hiramrodriguez14/Load-UI_MCU/mylib/WSON-6_2x2.step

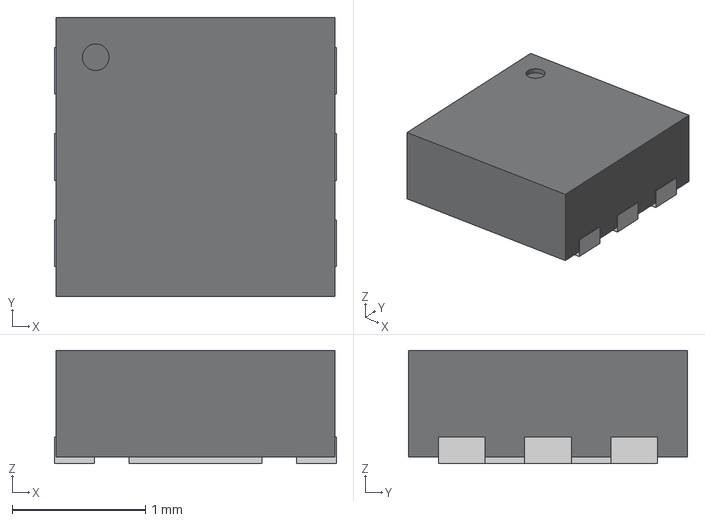
[picture p21: CAD file, 2026-04-30]
mylib/WSON-6_2x2.step
2.12 x 2.10 x 0.85 mm
Pads
