hiramrodriguez14/Load-UI_MCU/mylib/JST_3D/JST-XH4-SMD.step

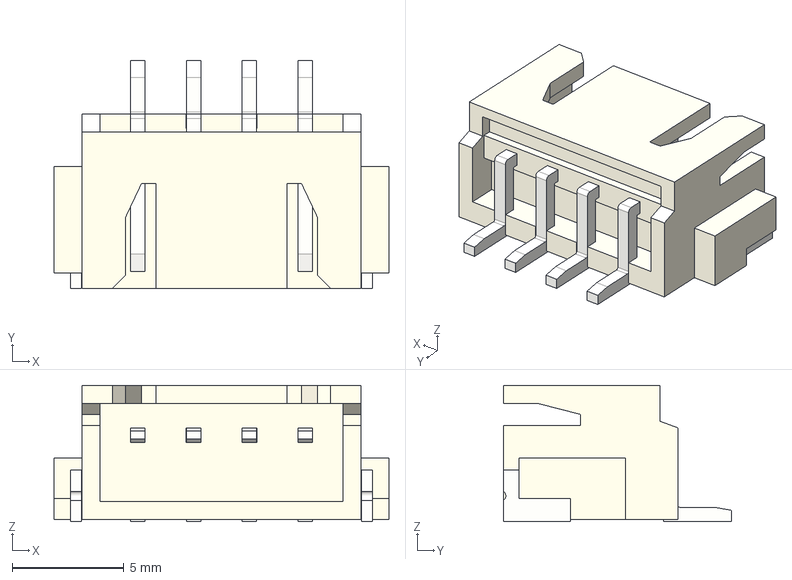
[picture p22: CAD file, 2026-04-30]
mylib/JST_3D/JST-XH4-SMD.step
15.0 x 10.2 x 6.10 mm
