hiramrodriguez14/Load-UI_MCU/mylib/kf128-screw-terminal-2-54-mm-pitch-1.snapshot.2/KF128 2.54mm/KF128-2.54-9P.step

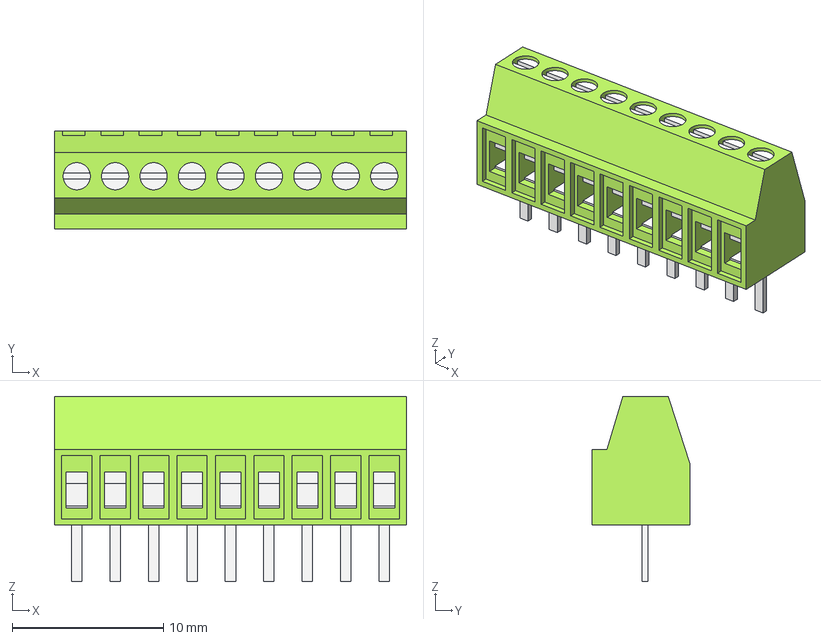
[picture p23: CAD file, 2026-04-30]
mylib/kf128-screw-terminal-2-54-mm-pitch-1.snapshot.2/KF128 2.54mm/KF128-2.54-9P.step
23.3 x 6.50 x 12.3 mm
Housing
PlasticBody
