hiramrodriguez14/Load-UI_MCU/mylib/LIB_TPS61046YFFR/TPS61046YFFR/3D/TPS61046YFFR.stp

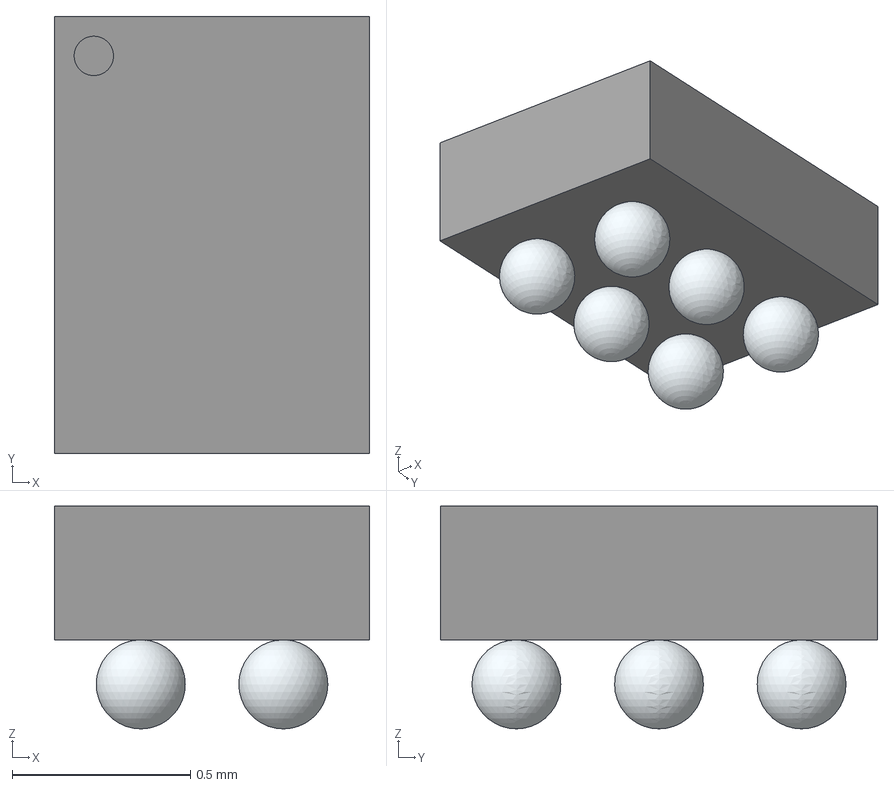
[picture p24: CAD file, 2026-04-30]
mylib/LIB_TPS61046YFFR/TPS61046YFFR/3D/TPS61046YFFR.stp
0.884 x 1.23 x 0.625 mm
